MOSH-Insa-Toulouse/MOSH_Pierre_LAURENS/Kicad/Projet_Kicad/Eeschema_shield.png

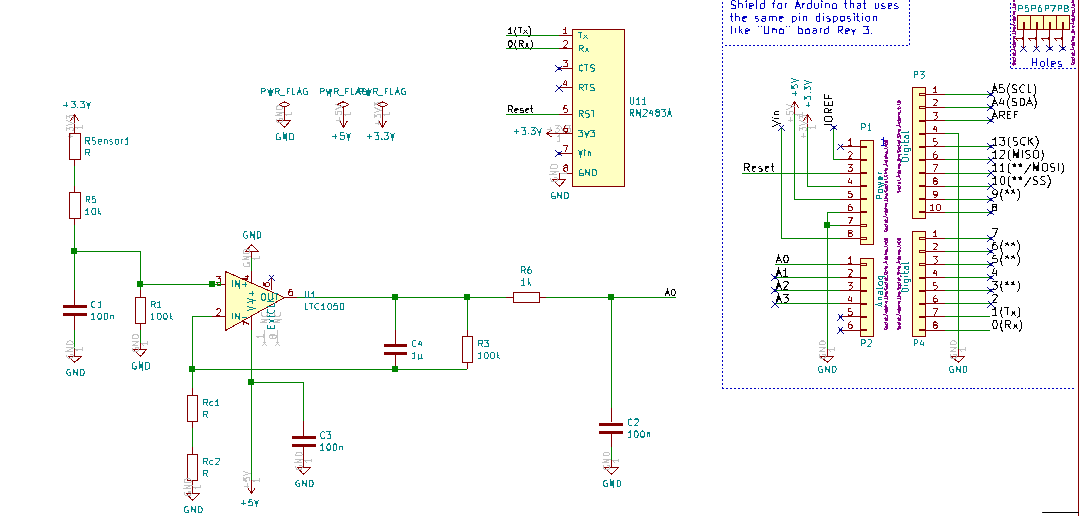
Kicad/Projet_Kicad/Eeschema_shield.png
