MOSH-Insa-Toulouse/MOSH_Pierre_LAURENS/Kicad/Projet_Kicad/PCB_shield_capteur.png

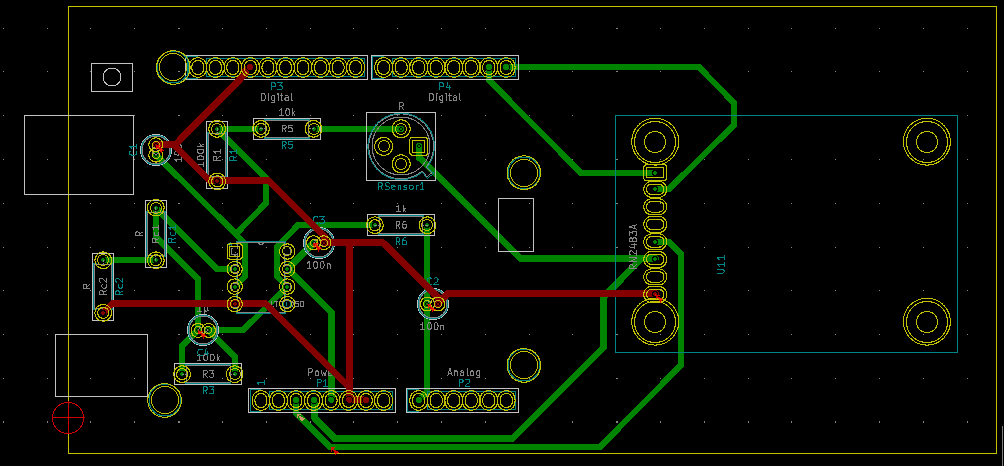
Kicad/Projet_Kicad/PCB_shield_capteur.png
