MOSH-Insa-Toulouse/MOSH_Pierre_LAURENS/Kicad/Projet_Kicad/Shield_avant_3D.png

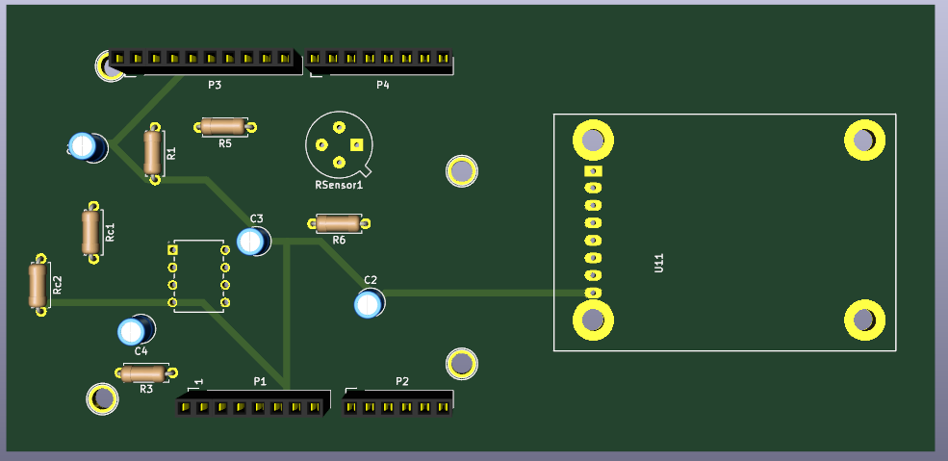
Kicad/Projet_Kicad/Shield_avant_3D.png
