MOSH-Insa-Toulouse/MOSH_Pierre_LAURENS/Kicad/Projet_Kicad_Aime_plan_masse/PCB_final_Aime_Capteur.png

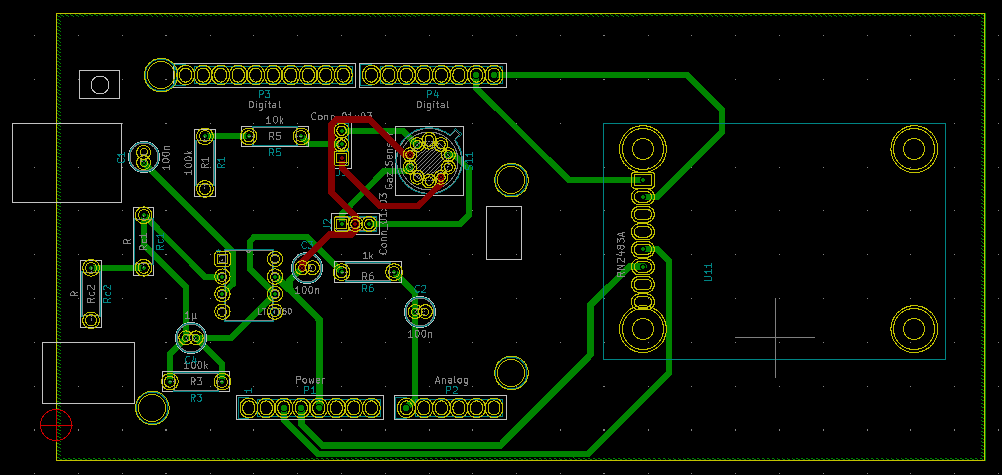
Kicad/Projet_Kicad_Aime_plan_masse/PCB_final_Aime_Capteur.png
