MOSH-Insa-Toulouse/MOSH_Pierre_LAURENS/Kicad/Projet_Kicad_Aime_plan_masse/PCB_final_Aime_Capteur_2.png

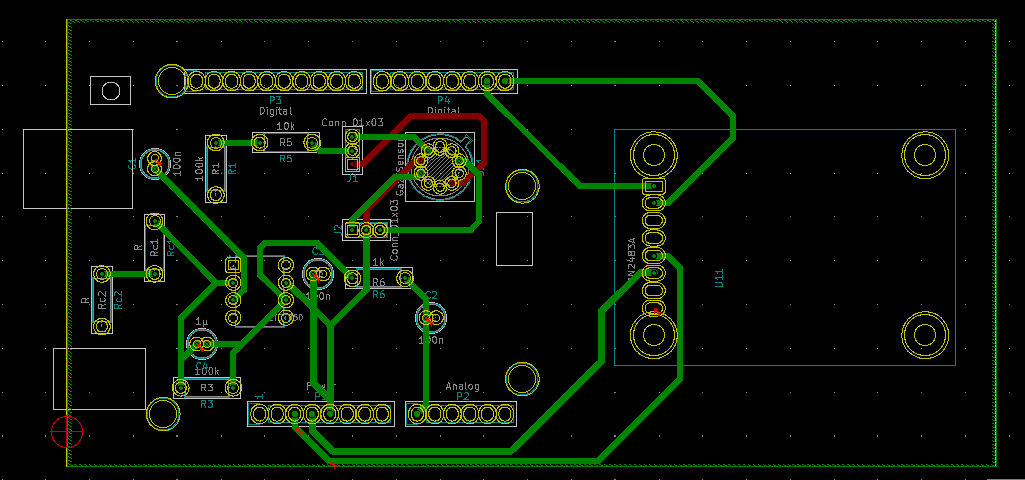
Kicad/Projet_Kicad_Aime_plan_masse/PCB_final_Aime_Capteur_2.png
