MOSH-Insa-Toulouse/MOSH_Pierre_LAURENS/LTspice/TPelectronique_Pierre_Laurens_Touzani.asc

C1: cap; 100n
C2: cap; 100n
C3: cap; 100n
C4: cap; 1µ
I1: current; PULSE(-50n -100n 0.1 0.1 0.1); AC 1
R1: res; 100k
R2: res; 1k
R3: res; 100K
R5: res; 10k
R6: res; 1K
U1: LTC1050
V2: voltage; 5
Named nets: 0, ADC, +5V, Isens
.tran 10n 10
.op
;.ac dec 200 0.01 100M
